mcer12/LEDDER-Stair-Lighting/Pictures/stairs_top.jpg

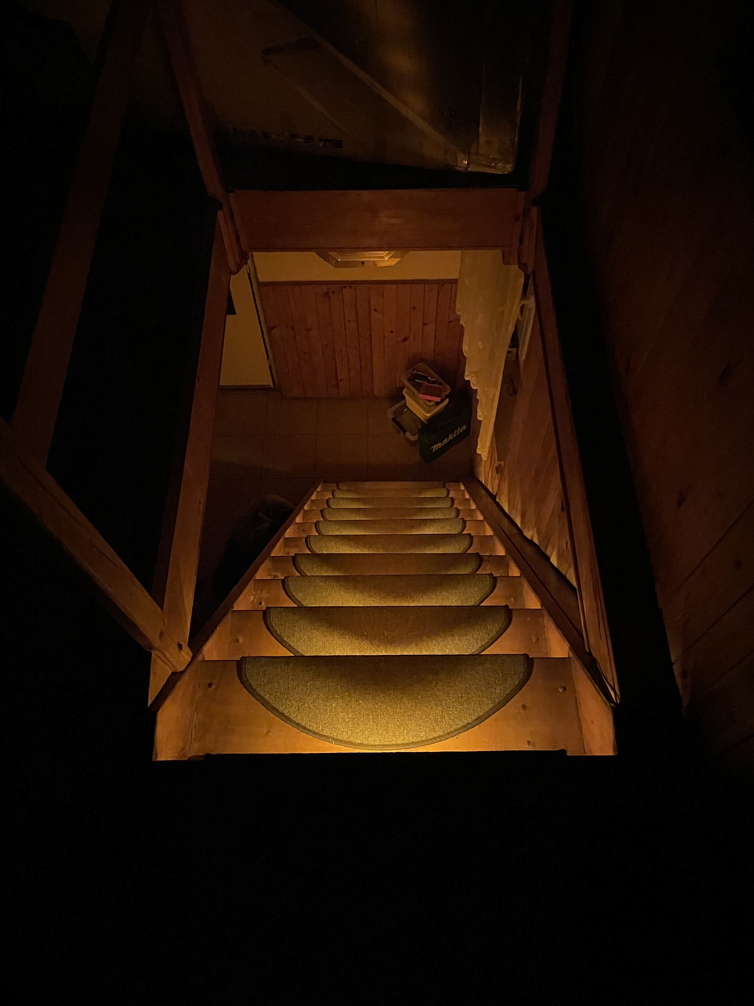
Pictures/stairs_top.jpg
