mcer12/LEDDER-Stair-Lighting/Sketch/STAIRS_LIGHT/gamma.h

// 8bit map with 12bit resolution
const uint16_t CIE[256] = {
    0,    2,    4,    5,    7,    9,   11,   12,   14,   16,   18,   20,   21,   23,   25,   27,
   28,   30,   32,   34,   36,   37,   39,   41,   43,   45,   47,   49,   52,   54,   56,   59,
   61,   64,   66,   69,   72,   75,   77,   80,   83,   87,   90,   93,   96,  100,  103,  107,
  111,  115,  118,  122,  126,  131,  135,  139,  144,  148,  153,  157,  162,  167,  172,  177,
  182,  187,  193,  198,  204,  209,  215,  221,  227,  233,  239,  246,  252,  259,  265,  272,
  279,  286,  293,  300,  308,  315,  323,  330,  338,  346,  354,  362,  371,  379,  388,  396,
  405,  414,  423,  432,  442,  451,  461,  470,  480,  490,  501,  511,  521,  532,  543,  553,
  564,  576,  587,  598,  610,  622,  634,  646,  658,  670,  683,  695,  708,  721,  734,  748,
  761,  775,  788,  802,  816,  831,  845,  860,  874,  889,  904,  920,  935,  951,  966,  982,
  999, 1015, 1031, 1048, 1065, 1082, 1099, 1116, 1134, 1152, 1170, 1188, 1206, 1224, 1243, 1262,
 1281, 1300, 1320, 1339, 1359, 1379, 1399, 1420, 1440, 1461, 1482, 1503, 1525, 1546, 1568, 1590,
 1612, 1635, 1657, 1680, 1703, 1726, 1750, 1774, 1797, 1822, 1846, 1870, 1895, 1920, 1945, 1971,
 1996, 2022, 2048, 2074, 2101, 2128, 2155, 2182, 2209, 2237, 2265, 2293, 2321, 2350, 2378, 2407,
 2437, 2466, 2496, 2526, 2556, 2587, 2617, 2648, 2679, 2711, 2743, 2774, 2807, 2839, 2872, 2905,
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
 3806, 3818, 3831, 3843, 3856, 3868, 3881, 3893, 3906, 3918, 3931, 3944, 3957, 3969, 3982, 3995,
 4008, 4021, 4034, 4046, 4059, 4072, 4085, 4098, 4111, 4125, 4138, 4151, 4164, 4177, 4190, 4204,
 4217, 4230, 4244, 4257, 4270, 4284, 4297, 4311, 4324, 4338, 4351, 4365, 4379, 4392, 4406, 4420,
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
};
