mcer12/LEDDER-Stair-Lighting/Pictures/imagy-image (5).jpg

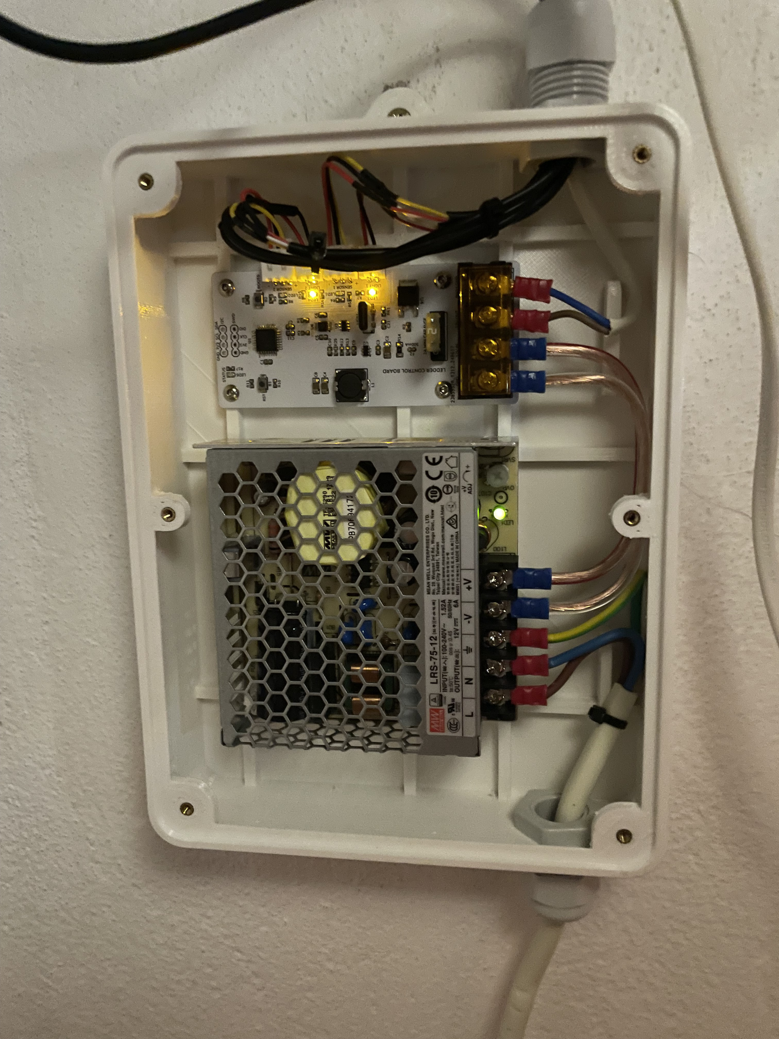
Pictures/imagy-image (5).jpg
